easai/LED-Panel-ESP12F/images/IMG_2773.jpeg

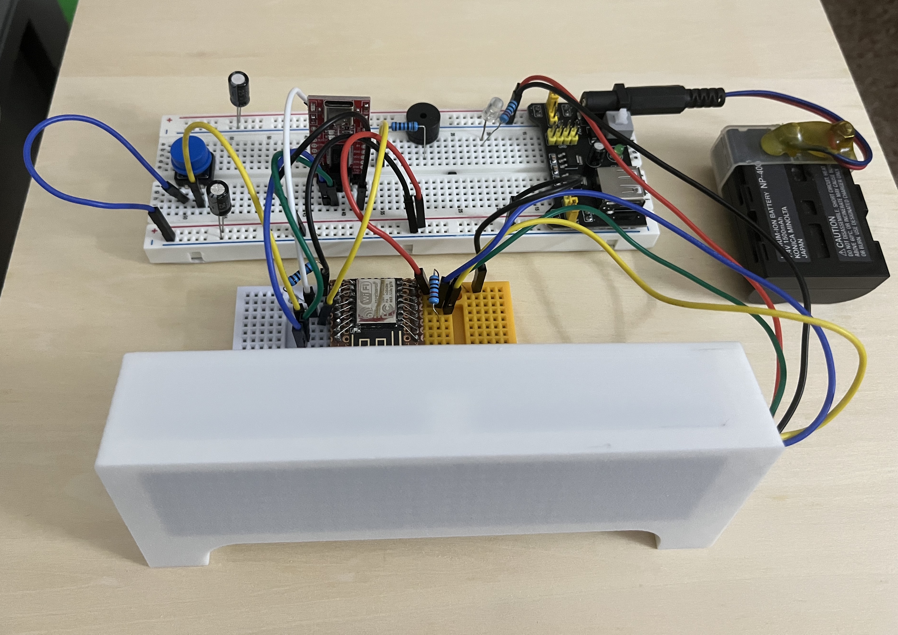
images/IMG_2773.jpeg
