easai/LED-Panel-ESP12F/images/IMG_2856.jpeg

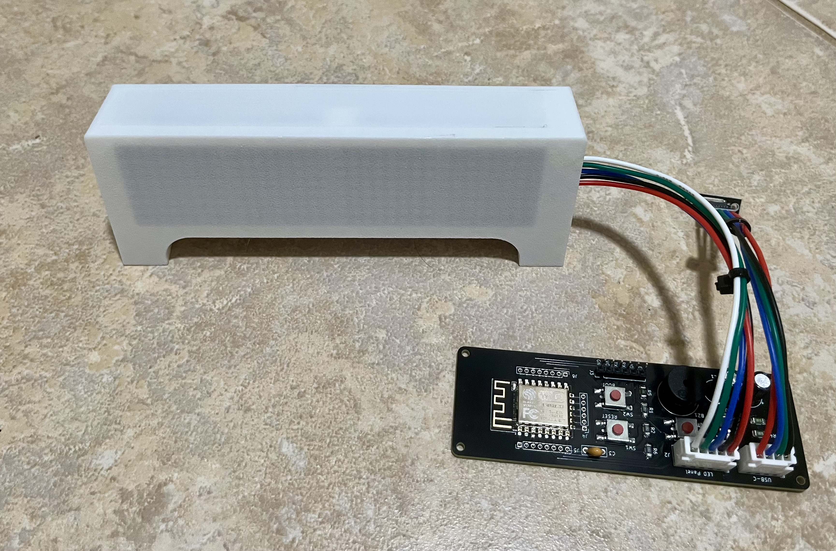
images/IMG_2856.jpeg
