easai/LED-Panel-ESP12F/images/Prototype (5).png

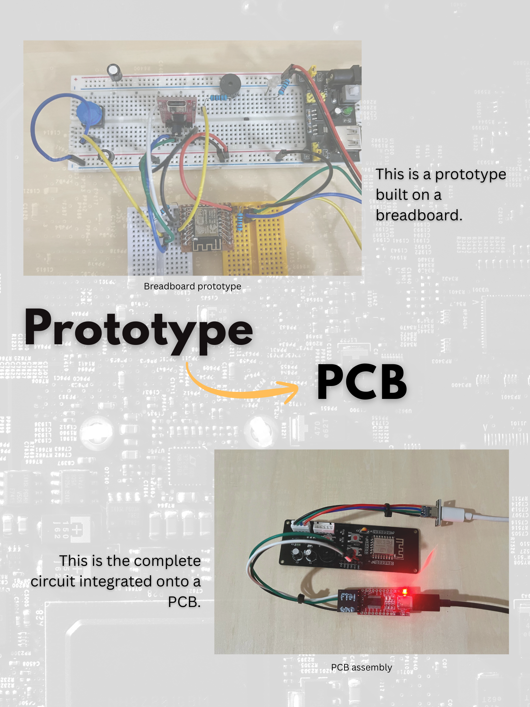
images/Prototype (5).png
